Erhannis/MaskTools/cutting_rig_small_bridge_print_two.stl

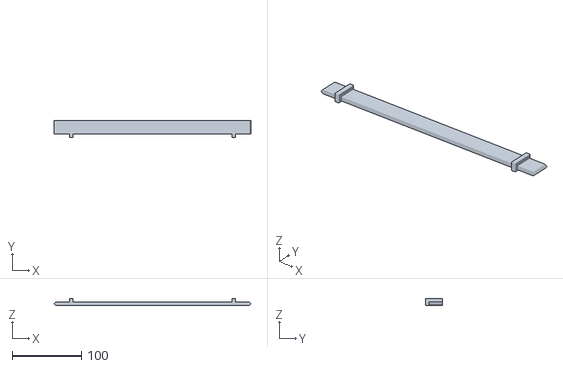
[picture p15: CAD file, 2020-04-03]
cutting_rig_small_bridge_print_two.stl
283.6 x 25.0 x 10.0
