Erhannis/MaskTools/1_inch_corner_spacer.stl

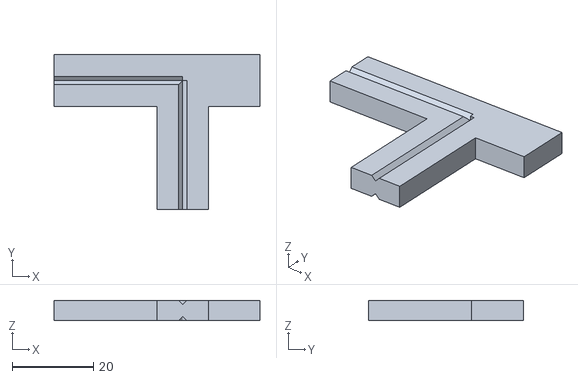
[picture p16: CAD file, 2020-04-03]
1_inch_corner_spacer.stl
50.8 x 38.1 x 5.00
