Erhannis/MaskTools/9_inch_corner_spacer.stl

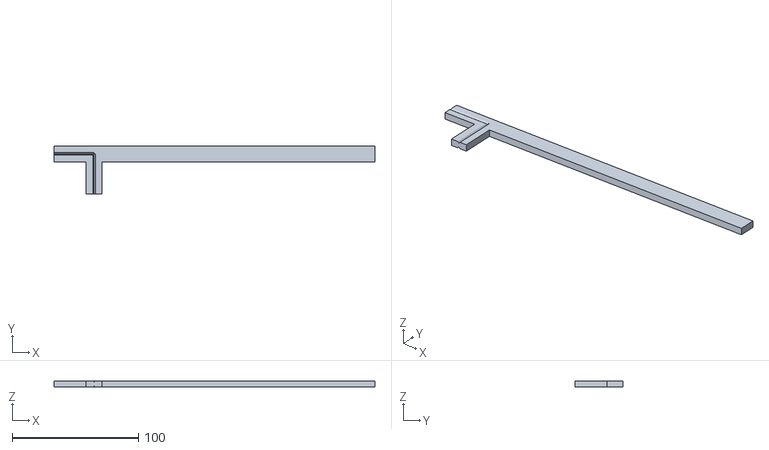
[picture p17: CAD file, 2020-04-03]
9_inch_corner_spacer.stl
254.0 x 38.1 x 5.00
