Erhannis/MaskTools/xacto_aligner.stl

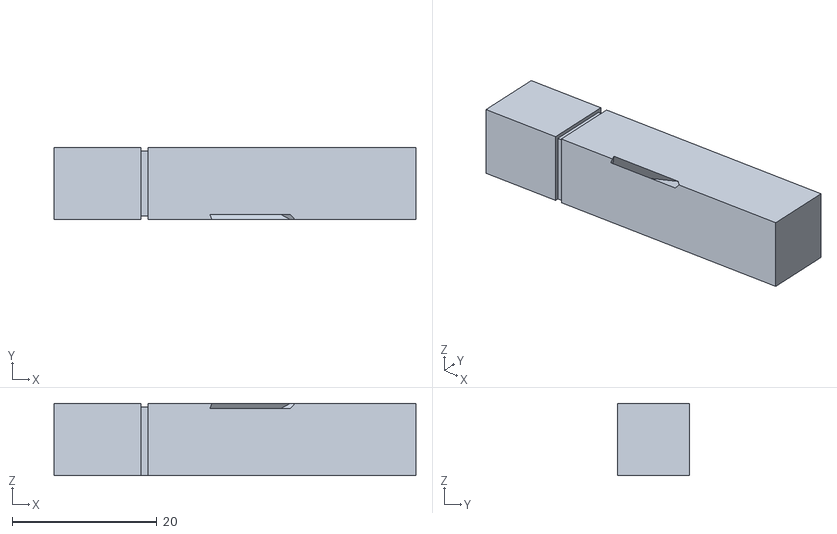
[picture p18: CAD file, 2020-04-02]
xacto_aligner.stl
50.0 x 10.0 x 10.0
