Erhannis/MaskTools/cutting_rig_edge_brace_print_two.stl

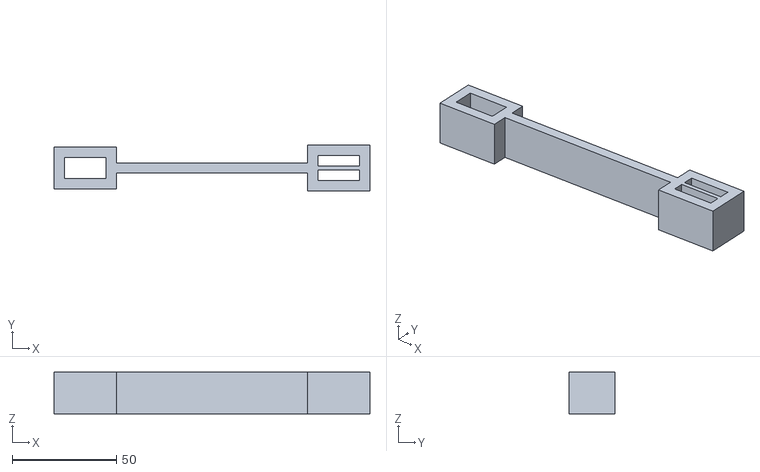
[picture p19: CAD file, 2020-04-02]
cutting_rig_edge_brace_print_two.stl
151.4 x 22.0 x 20.0
