Erhannis/MaskTools/9_inch_spacer_print_two.stl

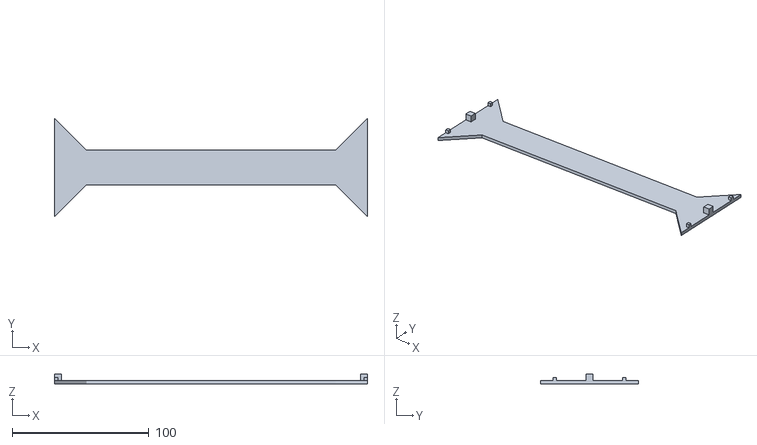
[picture p20: CAD file, 2020-04-01]
9_inch_spacer_print_two.stl
228.6 x 71.8 x 7.50
